jasonmzx/3D-Slit-Scanner_ESP32/data_camera_calibration/ESP_CAM_Dot_Pattern_Diffs/0_9.jpg

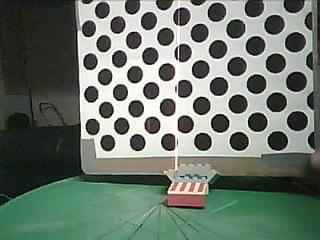
data_camera_calibration/ESP_CAM_Dot_Pattern_Diffs/0_9.jpg
