jasonmzx/3D-Slit-Scanner_ESP32/data_camera_calibration/ESP_Checkerboard/0_0-0000.jpg

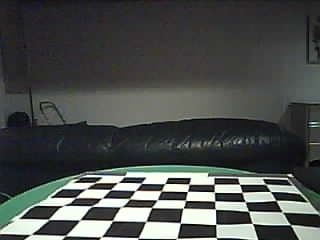
data_camera_calibration/ESP_Checkerboard/0_0-0000.jpg
