jasonmzx/3D-Slit-Scanner_ESP32/data_camera_calibration/ESP_Checkerboard/0_28-6000.jpg

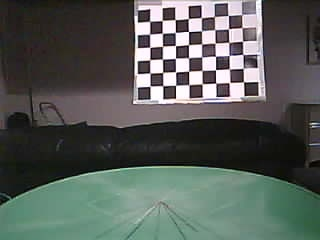
data_camera_calibration/ESP_Checkerboard/0_28-6000.jpg
