jasonmzx/3D-Slit-Scanner_ESP32/data_camera_calibration/ESP_Checkerboard/0_54-3400.jpg

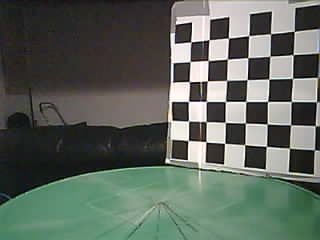
data_camera_calibration/ESP_Checkerboard/0_54-3400.jpg
