jasonmzx/3D-Slit-Scanner_ESP32/data_camera_calibration/ESP_Checkerboard/0_62-9200.jpg

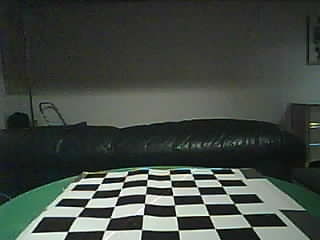
data_camera_calibration/ESP_Checkerboard/0_62-9200.jpg
