jasonmzx/3D-Slit-Scanner_ESP32/data_camera_calibration/ESP_Checkerboard/1_5-7200.jpg

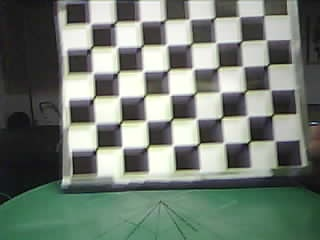
data_camera_calibration/ESP_Checkerboard/1_5-7200.jpg
