jasonmzx/3D-Slit-Scanner_ESP32/data_camera_calibration/ESP_Checkerboard/1_60-0600.jpg

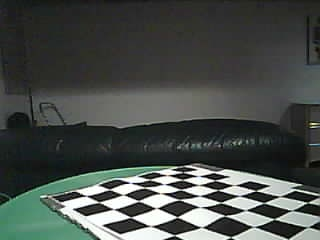
data_camera_calibration/ESP_Checkerboard/1_60-0600.jpg
