jasonmzx/3D-Slit-Scanner_ESP32/data_camera_calibration/ESP_Dot_Pattern/0_125-8400.jpg

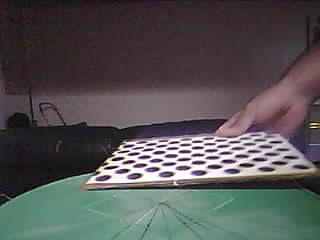
data_camera_calibration/ESP_Dot_Pattern/0_125-8400.jpg
