jasonmzx/3D-Slit-Scanner_ESP32/data_camera_calibration/ESP_Dot_Pattern/1_91-5200.jpg

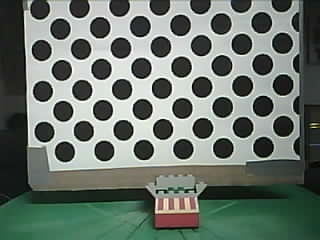
data_camera_calibration/ESP_Dot_Pattern/1_91-5200.jpg
