jasonmzx/3D-Slit-Scanner_ESP32/data_camera_calibration/ESP_Dot_Pattern/1_97-2400.jpg

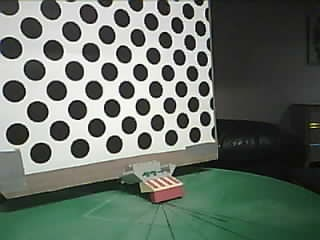
data_camera_calibration/ESP_Dot_Pattern/1_97-2400.jpg
