jasonmzx/3D-Slit-Scanner_ESP32/data_camera_calibration/example_cam/Im_L_5.png

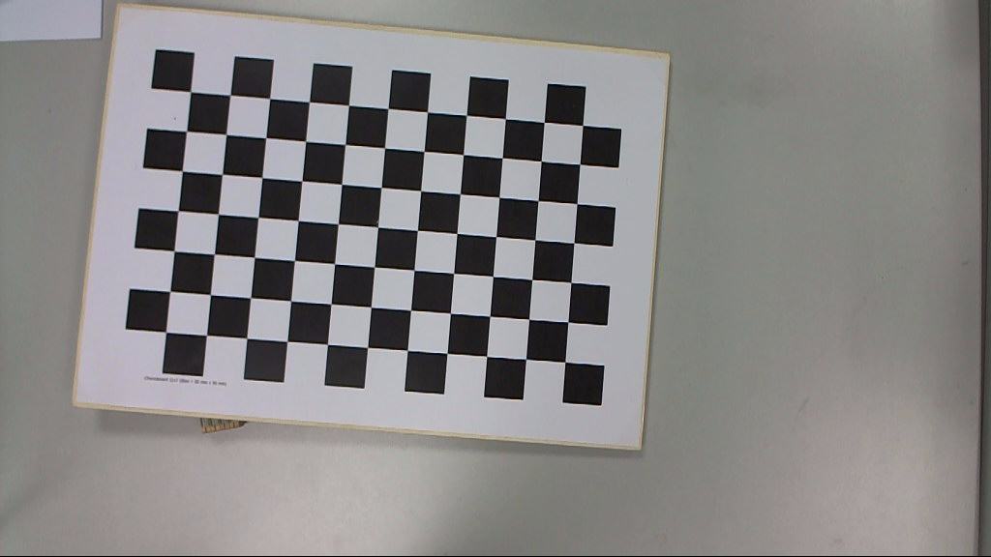
data_camera_calibration/example_cam/Im_L_5.png
