jasonmzx/3D-Slit-Scanner_ESP32/data_usable/mesh-matching-test-dataset/p3_elephant_2/0_247-7201.jpg

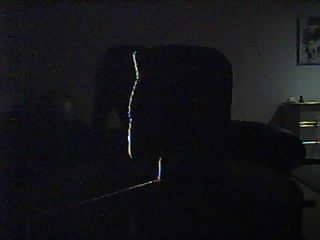
data_usable/mesh-matching-test-dataset/p3_elephant_2/0_247-7201.jpg
