jasonmzx/3D-Slit-Scanner_ESP32/data_usable/mesh-matching-test-dataset/p3_elephant_2/1_123-8600.jpg

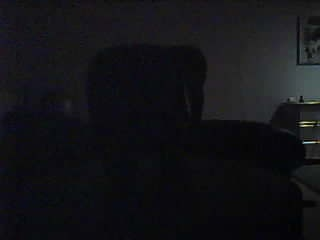
data_usable/mesh-matching-test-dataset/p3_elephant_2/1_123-8600.jpg
