jasonmzx/3D-Slit-Scanner_ESP32/data_usable/mesh-matching-test-dataset/p3_right_elephant_1/0_135-1200.jpg

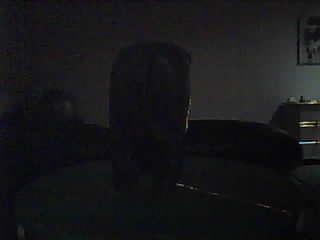
data_usable/mesh-matching-test-dataset/p3_right_elephant_1/0_135-1200.jpg
