jasonmzx/3D-Slit-Scanner_ESP32/data_usable/mesh-matching-test-dataset/p3_right_elephant_1/1_56-3000.jpg

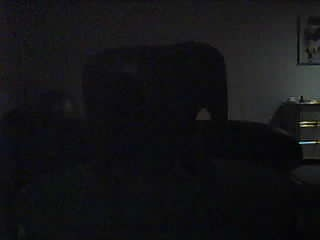
data_usable/mesh-matching-test-dataset/p3_right_elephant_1/1_56-3000.jpg
