jasonmzx/3D-Slit-Scanner_ESP32/data_usable/mesh-matching-test-dataset/p3_right_elephant_1/1_152-0100.jpg

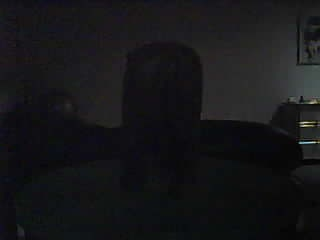
data_usable/mesh-matching-test-dataset/p3_right_elephant_1/1_152-0100.jpg
